Elecrow-RD/CrowPanel-3.5-HMI-ESP32-Display-480x320/arduino1.jpg

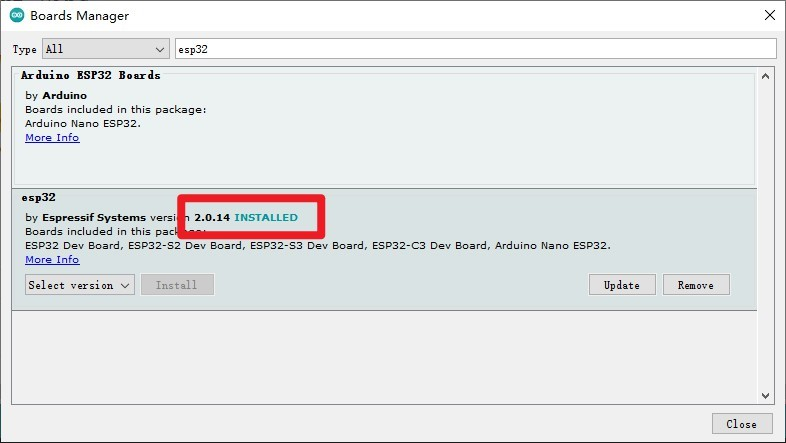
arduino1.jpg
