Elecrow-RD/CrowPanel-3.5-HMI-ESP32-Display-480x320/arduino2.jpg

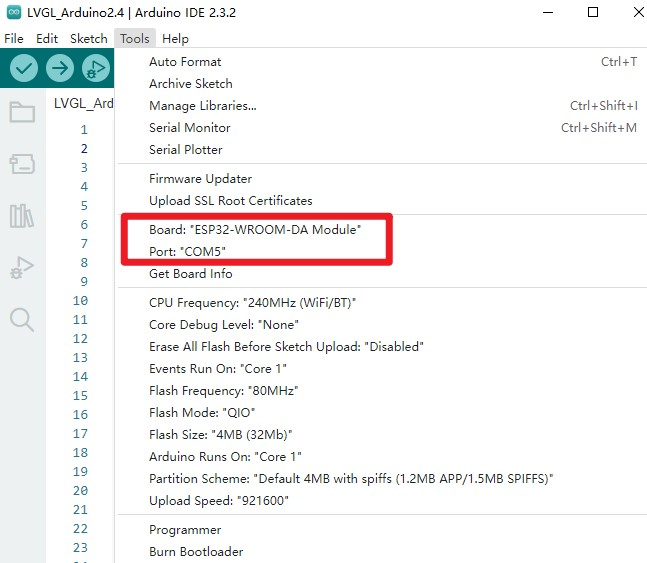
arduino2.jpg
