Elecrow-RD/CrowPanel-3.5-HMI-ESP32-Display-480x320/example/V2.2/Arduino/Course/LVGL_Arduino3.5/LVGL-Assets-480x320/background.png

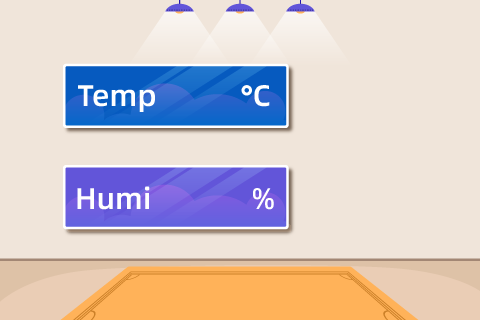
example/V2.2/Arduino/Course/LVGL_Arduino3.5/LVGL-Assets-480x320/background.png
