Elecrow-RD/CrowPanel-3.5-HMI-ESP32-Display-480x320/factory_firmare/flash1.jpg

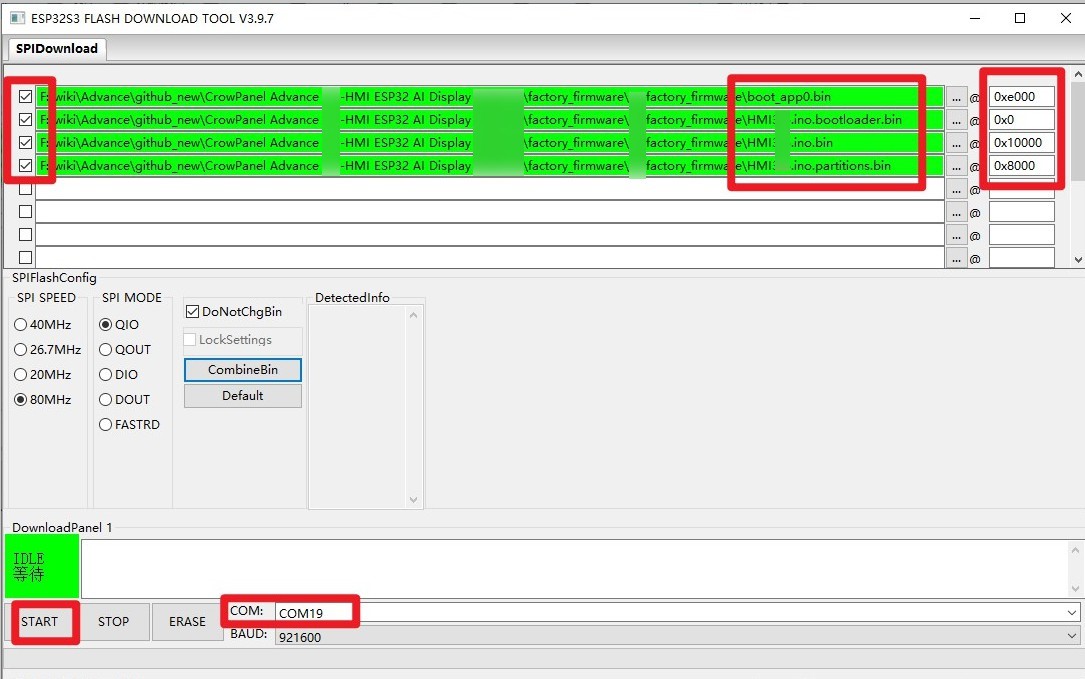
factory_firmare/flash1.jpg
