Elecrow-RD/CrowPanel-3.5-HMI-ESP32-Display-480x320/example/V1.0_and_V2.0_and_V2.1/ESP_IDF/CrowPanel_ESP32_3.5/components/lvgl-3/src/examples/assets/toppic.png

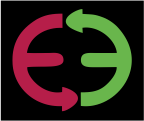
example/V1.0_and_V2.0_and_V2.1/ESP_IDF/CrowPanel_ESP32_3.5/components/lvgl-3/src/examples/assets/toppic.png
