Elecrow-RD/CrowPanel-3.5-HMI-ESP32-Display-480x320/example/V2.2/Micropython/Example2_T&H_Sensor/Example2_T&H_Sensor.py

import time
import DHT20
from machine import I2C, Pin
i2c = I2C(scl=Pin(21), sda=Pin(22))
sensor = DHT20.DHT20(i2c)

while True:
    sensor.read_dht20()
    print(sensor.dht20_temperature())
    print(sensor.dht20_humidity())
    time.sleep_ms(4000) 
