Elecrow-RD/CrowPanel-3.5-HMI-ESP32-Display-480x320/example/V1.0_and_V2.0_and_V2.1/Micropython/ESP32-3.5-MicroPython-Code/GPIO_Examples/button_led.py

from machine import Pin
import time

led = Pin(25, Pin.OUT)


button = Pin(21, Pin.IN, Pin.PULL_UP)


led.value(0)

while True:
    
    if not button.value():
        
        led.value(1)
    else:
        
        led.value(0)
    
    time.sleep(0.1)
